GJATHASEnterprises/Epitome/assets/step-walnut-product-sheet.png

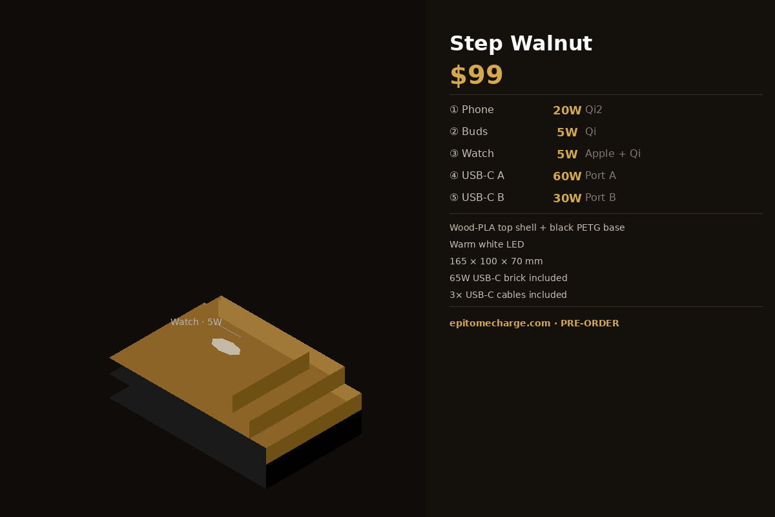
assets/step-walnut-product-sheet.png
